antonjan/rf_noise_antenna/gliffy/RF_Antenna_System_v2_0.png

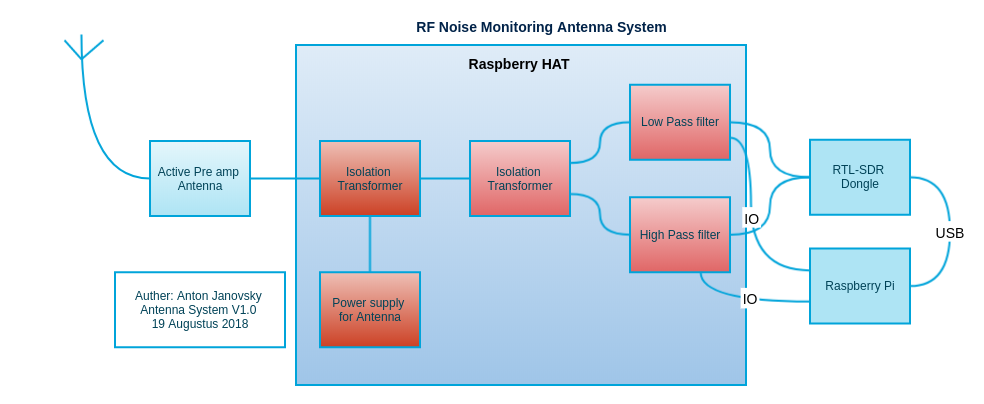
gliffy/RF_Antenna_System_v2_0.png
